fusuian/WiiBravo/WMCrypt.cpp

/*
* Wii RetroPad Adapter - Nintendo Wiimote adapter for retro-controllers!
* Copyright (c) 2018 ASAHI,Michiharu <fusuian@gmail.com>
* Based on code by Copyright (c) 2011 Bruno Freitas - bruno@brunofreitas.com
* and Copyright (C) 2008-2009 H�ctor Mart�n <hector@marcansoft.com>
*
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
* You should have received a copy of the GNU General Public License
* along with this program.  If not, see <http://www.gnu.org/licenses/>.
 */

#include <Arduino.h>
#include "WMCrypt.h"

unsigned char WMCrypt::wm_ft[8];
unsigned char WMCrypt::wm_sb[8];

const unsigned char WMCrypt::ans_tbl[7][6] PROGMEM = {
        {0xA8,0x77,0xA6,0xE0,0xF7,0x43},
        {0x5A,0x35,0x85,0xE2,0x72,0x97},
        {0x8F,0xB7,0x1A,0x62,0x87,0x38},
        { 0xD,0x67,0xC7,0xBE,0x4F,0x3E},
        {0x20,0x76,0x37,0x8F,0x68,0xB7},
        {0xA9,0x26,0x3F,0x2B,0x10,0xE3},
        {0x30,0x7E,0x90, 0xE,0x85, 0xA},
};

const unsigned char WMCrypt::tsbox[256] PROGMEM = {
        0x70,0x51,   3,0x86,0x40, 0xD,0x4F,0xEB,0x3E,0xCC,0xD1,0x87,0x35,0xBD,0xF5, 0xB,
        0x5E,0xD0,0xF8,0xF2,0xD5,0xE2,0x6C,0x31, 0xC,0xAD,0xFC,0x21,0xC3,0x78,0xC1,   6,
        0xC2,0x4C,0x55,0xE6,0x4A,0x34,0x48,0x11,0x1E,0xDA,0xE7,0x1A,0x84,0xA0,0x96,0xA7,
        0xE3,0x7F,0xAF,0x63,0x9C,0xFA,0x23,0x5B,0x79,0xC8,0x9E,0xBA,0xB2,0xC9,0x22,0x12,
        0x4B,0xB3,0xA1,0xB6,0x32,0x49,0xA2,0xE1,0x89,0x39,0x10,0x66,0xC5,   7,0x8F,0x54,
        0xEA,0x91,0xCA,0x3F,0xF9,0x19,0xF0,0xD7,0x46,0xBC,0x28,0x1B,0x61,0xE8,0x2F,0x6A,
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
                0x29, 0xF,0xF2,0x3B,0x51,0xC1,0xDE,0x5F,0xE5,0x2A,0x2F,0x99, 0xB,0x5D,0xA3,0x2B,
                0x4A,0xAB,0x95,0xA5,0xD3,0x58,0x56,0xEE,0x28,0x31,   0,0xCC,0x15,0x46,0xCA,0xE6,
                0x86,0x38,0x3C,0x65,0xF5,0xE3,0x9F,0xD6,0x5B,   9,0x49,0x83,0x70,0x2D,0x53,0xA9,
                0x7D,0xE2,0xC4,0xAC,0x8E,0x5E,0xB8,0x25,0xF4,0xB9,0x57,0xF3,0xF1,0x68,0x47,0xB2,
                0xA2,0x59,0x20,0xCE,0x34,0x79,0x5C,0x90, 0xE,0x1E,0xBE,0xD5,0x22,0x23,0xB1,0xC9,
                0x18,0x62,0x16,0x2E,0x91,0x3E,   7,0x8F,0xD8,0x3F,0x93,0x3D,0xD4,0x9B,0xDF,0x85,
                0x21,0xFB,0x11,0x74,0x97,0xC7,0xD7,0xDC,0x4C,0x19,0x45,0x98,0xE9,0x43,   2,0x4B,
                0xBC,0xC3,   4,0x9C,0x6B,0xF0,0x75,0x52,0xA7,0x26,0xF6,0xC5,0xBA,0xCF,0xB0,0xB7,
                0xAE,0x5A,0xA1,0xBF,   3,0x8B,0x80,0x12,0x6E, 0xC,0xEB,0xF9,0xC0,0x44,0x24,0xEF,
                0x10,0xF8,0xA8,0x8C,0xE8,0x7B,0xFF,0x9E,0x2C,0xCD,0x60,0x36,0x87,0xB5,0x94,0xA6,
                0x54,0x73,0x3A,0x14,0x4E,   1,0x1D,0xB6,0xFD,0x37,0x48,0x4D,0x39,0xCB,0xE0,0x32,
        }
};


unsigned char WMCrypt::ror8(const unsigned char a, const unsigned char b)
{
        return (a>>b) | ((a<<(8-b))&0xff);
}


void WMCrypt::genkey(const unsigned char* const rand, const unsigned char idx, unsigned char* const key)
{
        const unsigned char* const ans = WMCrypt::ans_tbl[idx];
        unsigned char t0[10];

        for(int i=0; i<10; ++i)
                t0[i] = pgm_read_byte(&WMCrypt::tsbox[rand[i]]);

        key[0] = ((WMCrypt::ror8((pgm_read_byte(&ans[0])^t0[5]),(t0[2]%8)) - t0[9]) ^ t0[4]);
        key[1] = ((WMCrypt::ror8((pgm_read_byte(&ans[1])^t0[1]),(t0[0]%8)) - t0[5]) ^ t0[7]);
        key[2] = ((WMCrypt::ror8((pgm_read_byte(&ans[2])^t0[6]),(t0[8]%8)) - t0[2]) ^ t0[0]);
        key[3] = ((WMCrypt::ror8((pgm_read_byte(&ans[3])^t0[4]),(t0[7]%8)) - t0[3]) ^ t0[2]);
        key[4] = ((WMCrypt::ror8((pgm_read_byte(&ans[4])^t0[1]),(t0[6]%8)) - t0[3]) ^ t0[4]);
        key[5] = ((WMCrypt::ror8((pgm_read_byte(&ans[5])^t0[7]),(t0[8]%8)) - t0[5]) ^ t0[9]);
}


void WMCrypt::gentabs(const unsigned char* const rand, const unsigned char* const key, const unsigned char idx, unsigned char* const ft, unsigned char* const sb)
{
        ft[0] = pgm_read_byte(&WMCrypt::sboxes[idx][key[4]]) ^ pgm_read_byte(&WMCrypt::sboxes[(idx+1)%8][rand[3]]);
        ft[1] = pgm_read_byte(&WMCrypt::sboxes[idx][key[2]]) ^ pgm_read_byte(&WMCrypt::sboxes[(idx+1)%8][rand[5]]);
        ft[2] = pgm_read_byte(&WMCrypt::sboxes[idx][key[5]]) ^ pgm_read_byte(&WMCrypt::sboxes[(idx+1)%8][rand[7]]);
        ft[3] = pgm_read_byte(&WMCrypt::sboxes[idx][key[0]]) ^ pgm_read_byte(&WMCrypt::sboxes[(idx+1)%8][rand[2]]);
        ft[4] = pgm_read_byte(&WMCrypt::sboxes[idx][key[1]]) ^ pgm_read_byte(&WMCrypt::sboxes[(idx+1)%8][rand[4]]);
        ft[5] = pgm_read_byte(&WMCrypt::sboxes[idx][key[3]]) ^ pgm_read_byte(&WMCrypt::sboxes[(idx+1)%8][rand[9]]);
        ft[6] = pgm_read_byte(&WMCrypt::sboxes[idx][rand[0]]) ^ pgm_read_byte(&WMCrypt::sboxes[(idx+1)%8][rand[6]]);
        ft[7] = pgm_read_byte(&WMCrypt::sboxes[idx][rand[1]]) ^ pgm_read_byte(&WMCrypt::sboxes[(idx+1)%8][rand[8]]);

        sb[0] = pgm_read_byte(&WMCrypt::sboxes[idx][key[0]]) ^ pgm_read_byte(&WMCrypt::sboxes[(idx+1)%8][rand[1]]);
        sb[1] = pgm_read_byte(&WMCrypt::sboxes[idx][key[5]]) ^ pgm_read_byte(&WMCrypt::sboxes[(idx+1)%8][rand[4]]);
        sb[2] = pgm_read_byte(&WMCrypt::sboxes[idx][key[3]]) ^ pgm_read_byte(&WMCrypt::sboxes[(idx+1)%8][rand[0]]);
        sb[3] = pgm_read_byte(&WMCrypt::sboxes[idx][key[2]]) ^ pgm_read_byte(&WMCrypt::sboxes[(idx+1)%8][rand[9]]);
        sb[4] = pgm_read_byte(&WMCrypt::sboxes[idx][key[4]]) ^ pgm_read_byte(&WMCrypt::sboxes[(idx+1)%8][rand[7]]);
        sb[5] = pgm_read_byte(&WMCrypt::sboxes[idx][key[1]]) ^ pgm_read_byte(&WMCrypt::sboxes[(idx+1)%8][rand[8]]);
        sb[6] = pgm_read_byte(&WMCrypt::sboxes[idx][rand[3]]) ^ pgm_read_byte(&WMCrypt::sboxes[(idx+1)%8][rand[5]]);
        sb[7] = pgm_read_byte(&WMCrypt::sboxes[idx][rand[2]]) ^ pgm_read_byte(&WMCrypt::sboxes[(idx+1)%8][rand[6]]);
}

/* Generate key from the 0x40-0x4c data in g_RegExt */
void WMCrypt::wiimote_gen_key(const unsigned char* const keydata)
{
        unsigned char rand[10];
        unsigned char skey[6];
        unsigned char testkey[6];
        int idx;

        for (int i=0; i<10; ++i)
                rand[9-i] = keydata[i];
        for (int i=0; i<6; ++i)
                skey[5-i] = keydata[i+10];


        for(idx = 0; idx < 7; ++idx)
        {
                genkey(rand, idx, testkey);
                if (0 == memcmp(testkey, skey, 6))
                        break;
        }
        // default case is idx = 7 which is valid (homebrew uses it for the 0x17 case)

        gentabs(rand, skey, idx, WMCrypt::wm_ft, WMCrypt::wm_sb);

        // for homebrew, ft and sb are all 0x97 which is equivalent to 0x17
}
