fusuian/WiiBravo/portmacro.h

/**
 * portmacro.h - fast digitalWrite for Arduino Uno / Nano / Pro mini
 * Copyright (c) 2018 ASAHI,Michiharu <fusuian@gmail.com>
 *
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
 * You should have received a copy of the GNU General Public License
 * along with portmacro.h.  If not, see <http://www.gnu.org/licenses/>.
 */

#ifndef __PORTMACRO_H__
#define __PORTMACRO_H__

#define PORT(n) ( (n <=  7)? PORTD : \
                ( (n <= 13)? PORTB : \
                ( (n <= 19)? PORTC : PORTB)))

#define PIN(n) ( (n <=  7)? PIND : \
               ( (n <= 13)? PINB : \
               ( (n <= 19)? PINC : PINB)))

#define REG(n)  ( (n <=  7)? (n) : \
                ( (n <= 13)? (n - 8) : \
                ( (n <= 19)? (n - 14) : (13 - 8) )))

// set pin HIGH
#define portOn(p)  ( PORT(p) |=  _BV(REG(p)) )
// set pin LOW
#define portOff(p) ( PORT(p) &= ~_BV(REG(p)) )
// check pin state
#define isPin(p)  ( (PIN(p) & _BV(REG(p))) == 0 )

#endif // __PORTMACRO_H__
